JayesonLS/8-bit-ide/Firmware/Common/IoConfig.cpp

// Copyright (C) 2021 Titanium Studios Pty Ltd 

#include <pico/stdlib.h>
#include "IoConfig.h"

/*static*/ void IoConfig::PreInitialzieIo()
{
    // We don't call gpio_init() for two reasons. First
    // is that it will be a little slower as it only does
    // one pin at a time. Second is that it will switch
    // everything to inputs first while we want some to 
    // be outputs. If we are doing some kind of reset and
    // the registers have not been set to default values,
    // then better to assume some pins might already be in
    // the state that we want.

    // The order here is chosen on purpose.
    // First, disable any outputs that should not be inputs,
    // then clear/set in/out values as needed, then enable
    // outputs.
    sio_hw->gpio_oe_clr = INITIAL_INPUTS;
    sio_hw->gpio_clr = INITIAL_INPUTS | INITIAL_OUTPUTS_LOW;
    sio_hw->gpio_set = INITIAL_OUTPUTS_HIGH;
    sio_hw->gpio_oe_set = INITIAL_OUTPUTS;

    // To start, configure any pins we are using as SIO's.
    // gpio_set_function enables inputs/outputs to function 
    // It also clears all of the GPIOx_CONTROL register
    // (signal inversions, etc.) except for setting the
    // function to SIO. 
    for (uint pinIndex = 0; pinIndex < 32; pinIndex++)
    {
        if (INITIAL_INPUTS_AND_OUTPUTS & (1 << pinIndex))
        {
            gpio_set_function(pinIndex, GPIO_FUNC_SIO);
        }

        // Disable the pullups resistors for pins with external pullups.
        // No need to load the pin any further.
        if (EXTERNAL_PULL_PINS & (1 << pinIndex))
        {
            gpio_disable_pulls(pinIndex);            
        }
    }
}

/*static*/ void IoConfig::FinishInitializeIo()
{
    // TODO: Move IRQ and DRQ inversion from XtBus to here.

}
